GeckoOfDeath/GamerPad/GamerPad/Images/CAD Pictures/1.png

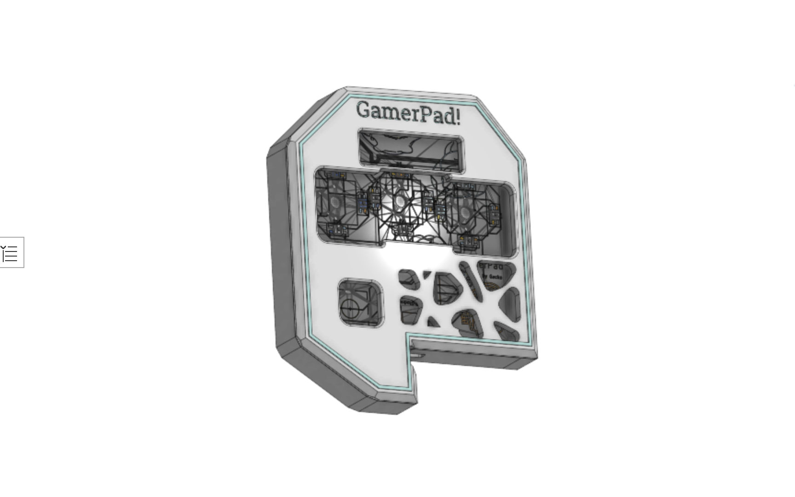
GamerPad/Images/CAD Pictures/1.png
